fieldfish/HoloPet/mechanical/compact_base_v2/fit_test/screen_body_fit_coupon.stl

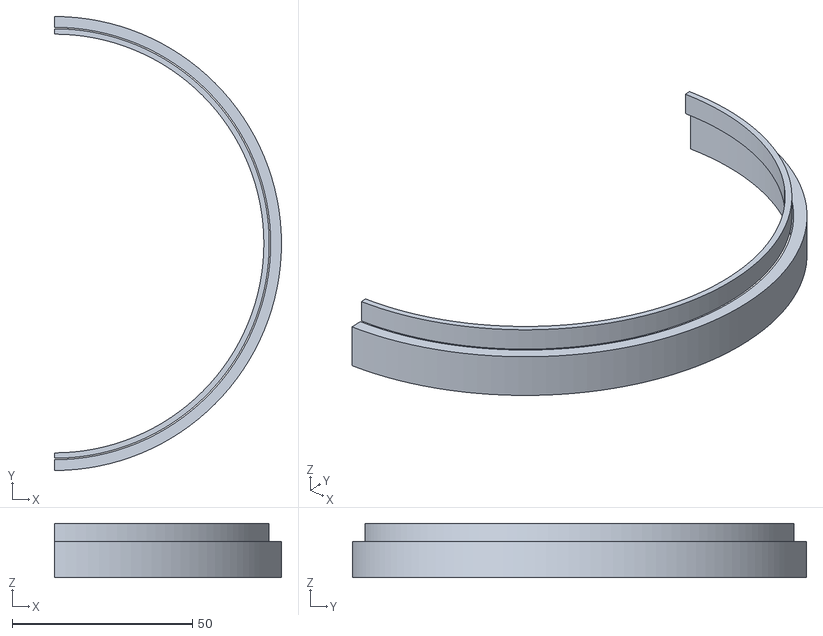
[picture p27: CAD file, 2026-09-20, an earlier design]
mechanical/compact_base_v2/fit_test/screen_body_fit_coupon.stl
63.0 x 126.0 x 15.0
