fieldfish/HoloPet/mechanical/compact_base_v2/stl/07_ec11_knob.stl

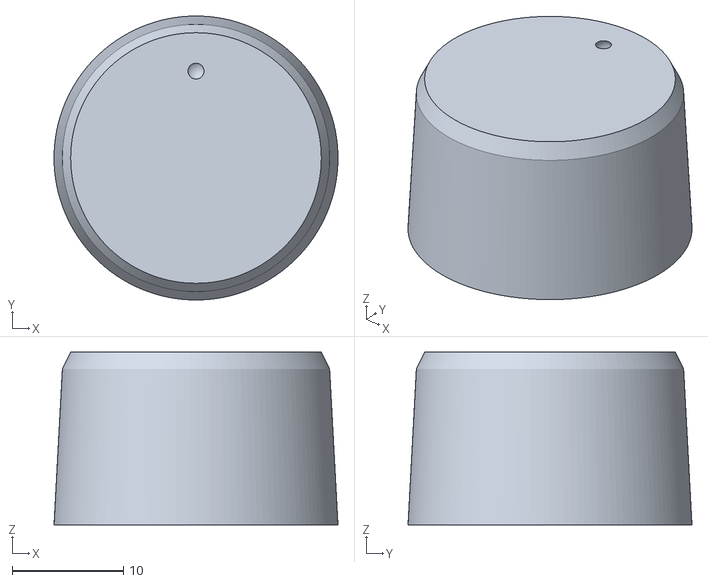
[picture p28: CAD file, 2026-09-20, an earlier design]
mechanical/compact_base_v2/stl/07_ec11_knob.stl
25.5 x 25.5 x 15.5
