fieldfish/HoloPet/mechanical/compact_base_v3_1/stl/02_top_collar.stl

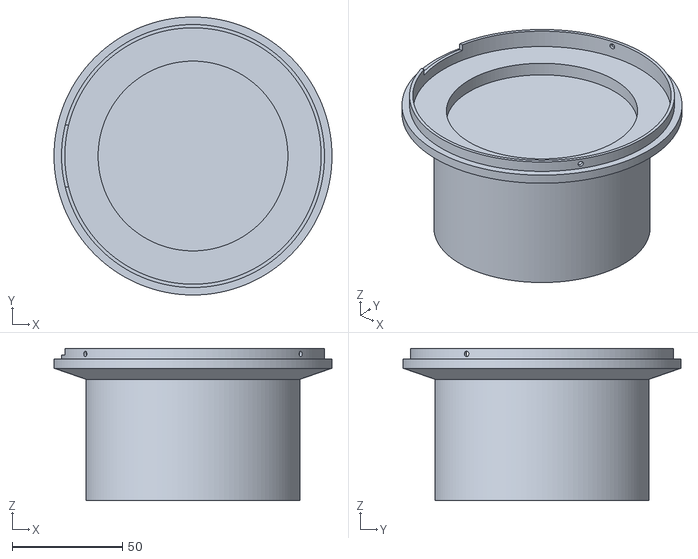
[picture p29: CAD file, 2026-09-20, an earlier design]
mechanical/compact_base_v3_1/stl/02_top_collar.stl
126.0 x 126.0 x 69.0
